dunkelstern/electret_preamp/ltspice/preamp_lm318.asc

C1: cap; 2p; V=25 Irms=0 Rser=0 Lser=0 mfg="Murata" pn="GRM0335C1E1R0CA01" type="C0G"
C3: polcap; 2.2u; V=16 Irms=35m Rser=2.8 Lser=0
C5: polcap; 1u; V=50 Irms=12m Rser=22 Lser=0
C6: polcap; 10u; V=16 Irms=35m Rser=2.8 Lser=0
Mic: voltage; ""; AC 0.010; Rser=2.2k
MicBias: voltage; 2
R1: res; 6.2k; tol=1 pwr=0.1
R2: res; 180k; tol=1 pwr=0.1
R3: res; 100K; tol=1 pwr=0.1
R4: res; 47; tol=1 pwr=0.1
R5: res; 100K; tol=1 pwr=0.1
R6: res; 100K; tol=1 pwr=0.1
U1: LM318TI_SN
V1: voltage; 5.3
Named nets: 0, VCC, VOut
.ac lin 10000 25 20000
